009rishab-afk/CD-Mesh_S3-Meshtastic/Hardware/IMG/BAT-CHG.jpg

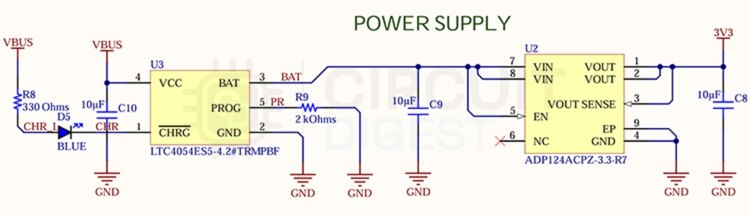
Hardware/IMG/BAT-CHG.jpg
