009rishab-afk/CD-Mesh_S3-Meshtastic/Hardware/IMG/Chat-Overview.png

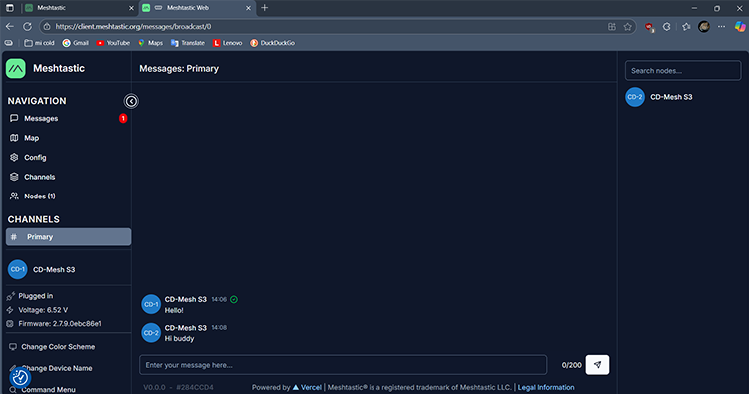
Hardware/IMG/Chat-Overview.png
