009rishab-afk/CD-Mesh_S3-Meshtastic/Hardware/IMG/Env-Select.png

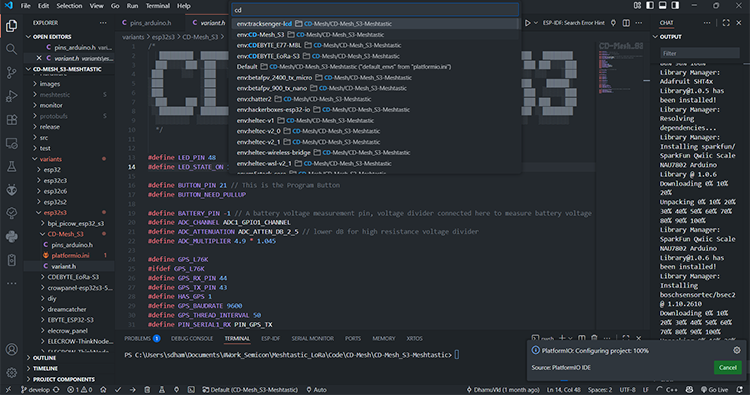
Hardware/IMG/Env-Select.png
