009rishab-afk/CD-Mesh_S3-Meshtastic/Hardware/IMG/ESP32S3-MCU.jpg

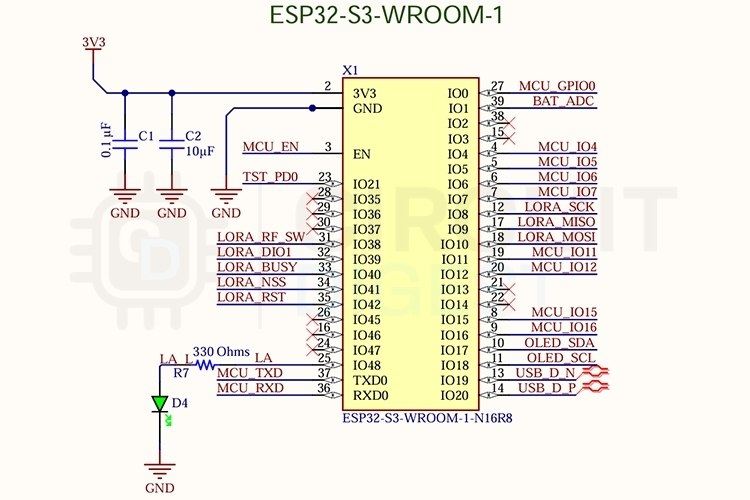
Hardware/IMG/ESP32S3-MCU.jpg
