009rishab-afk/CD-Mesh_S3-Meshtastic/Hardware/IMG/GPIO-Expander.jpg

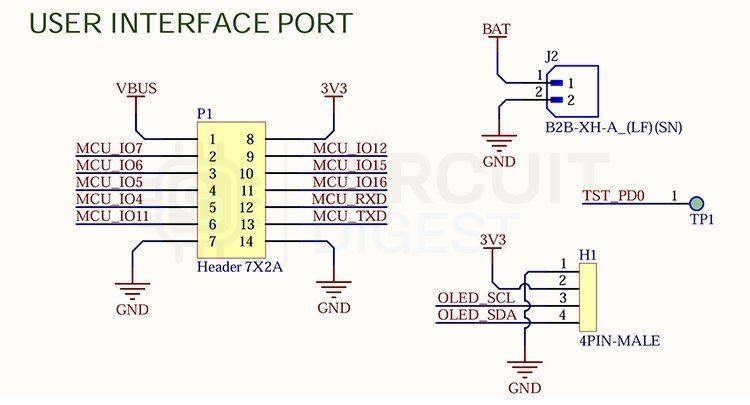
Hardware/IMG/GPIO-Expander.jpg
