009rishab-afk/CD-Mesh_S3-Meshtastic/Hardware/IMG/Interface.png

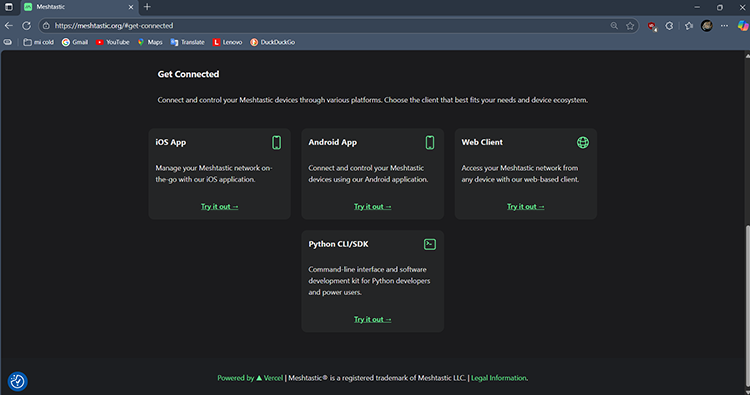
Hardware/IMG/Interface.png
