009rishab-afk/CD-Mesh_S3-Meshtastic/Hardware/IMG/JLCPCB.jpg

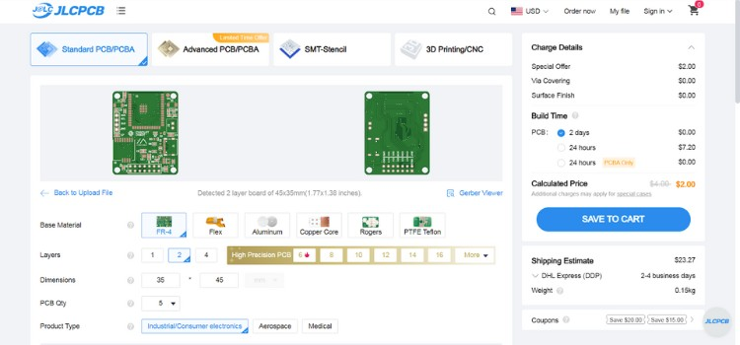
Hardware/IMG/JLCPCB.jpg
