009rishab-afk/CD-Mesh_S3-Meshtastic/Hardware/IMG/Part-View.jpg

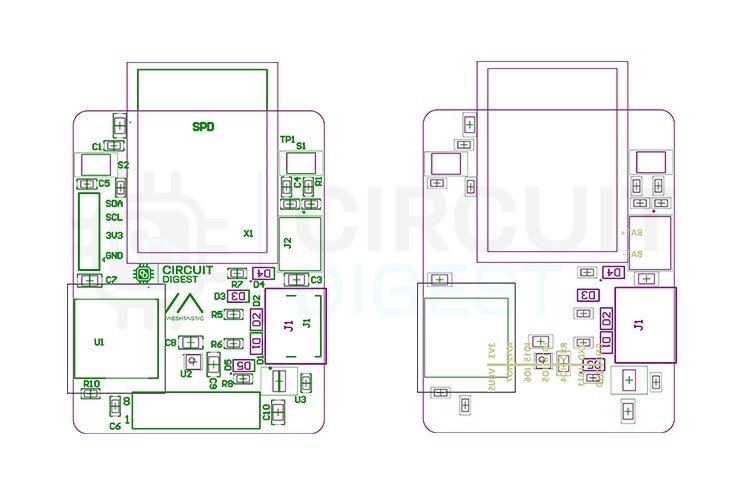
Hardware/IMG/Part-View.jpg
