009rishab-afk/CD-Mesh_S3-Meshtastic/Hardware/IMG/PCB-Overview.jpg

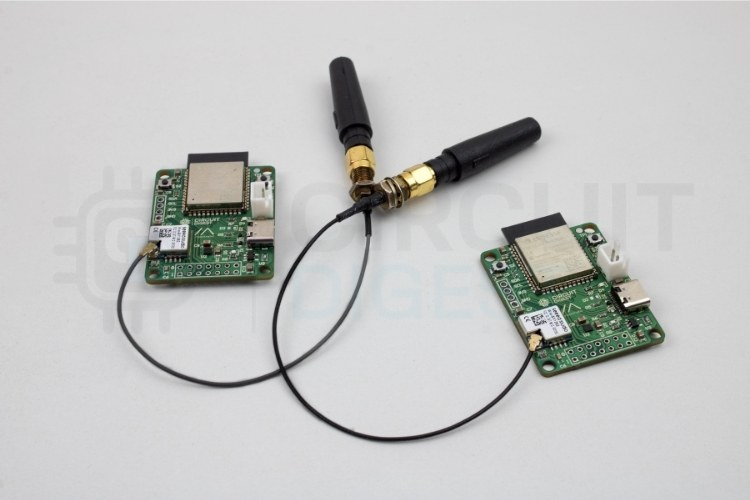
Hardware/IMG/PCB-Overview.jpg
