009rishab-afk/CD-Mesh_S3-Meshtastic/Hardware/IMG/Port-Select.png

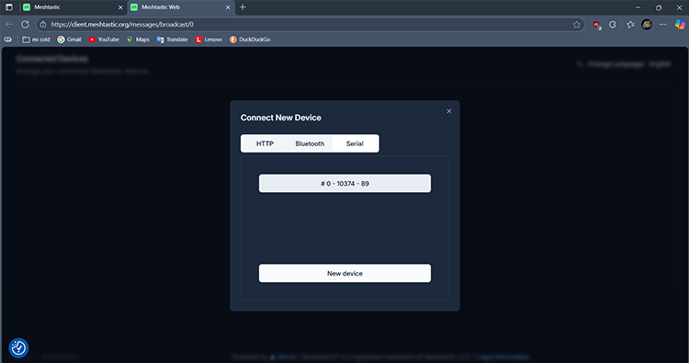
Hardware/IMG/Port-Select.png
