009rishab-afk/CD-Mesh_S3-Meshtastic/Hardware/IMG/Top-and-Bottom-Plane.jpg

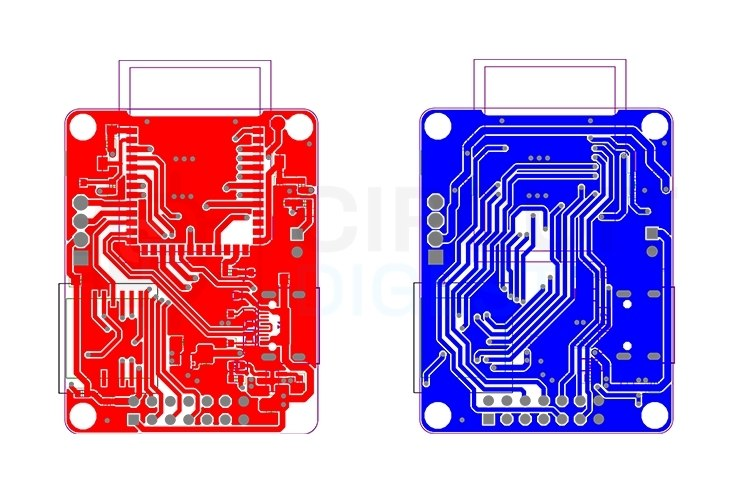
Hardware/IMG/Top-and-Bottom-Plane.jpg
