009rishab-afk/CD-Mesh_S3-Meshtastic/Hardware/IMG/WIO-SX1262.jpg

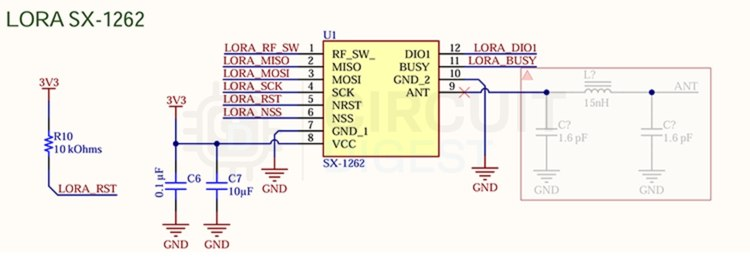
Hardware/IMG/WIO-SX1262.jpg
