009rishab-afk/CD-Mesh_S3-Meshtastic/Hardware/PCB/PCB_Board/Layers/Fab-6.png

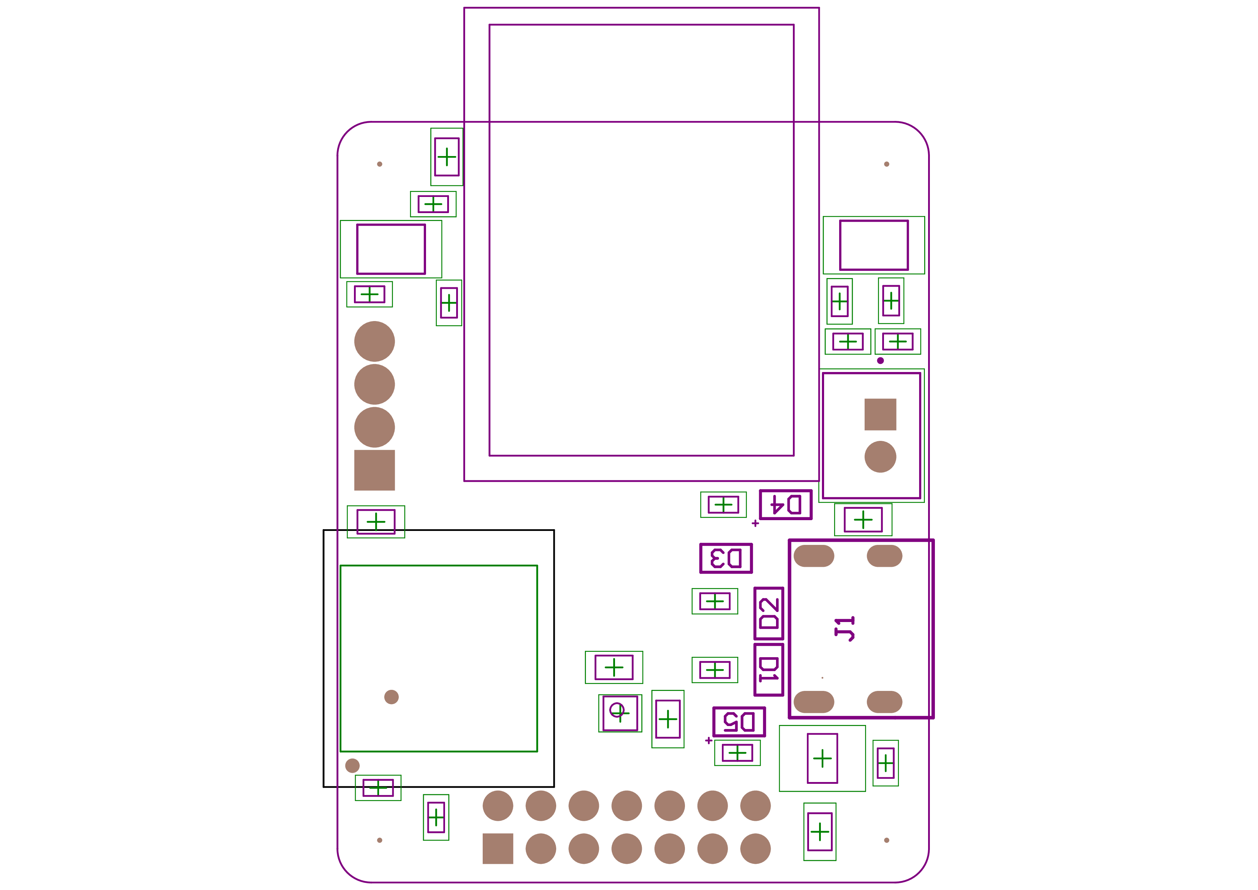
Hardware/PCB/PCB_Board/Layers/Fab-6.png
