009rishab-afk/CD-Mesh_S3-Meshtastic/Hardware/PCB/PCB_Board/PCB3-ESP32S3.png

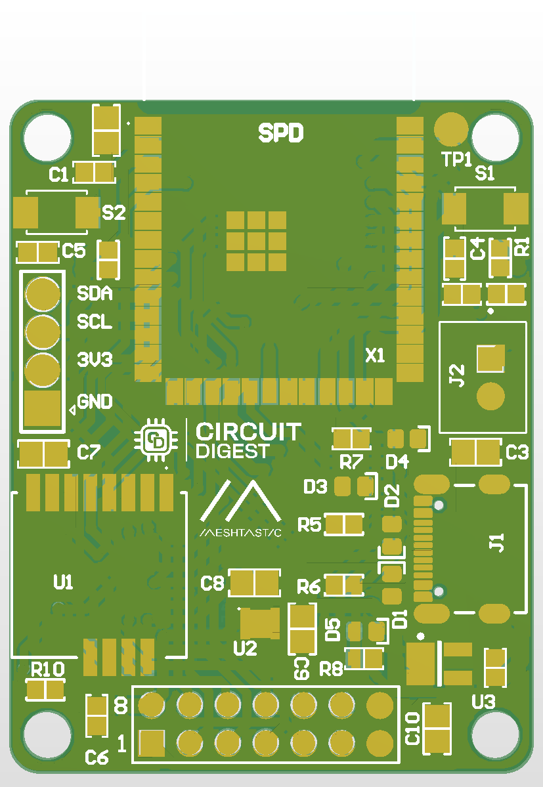
Hardware/PCB/PCB_Board/PCB3-ESP32S3.png
