009rishab-afk/CD-Mesh_S3-Meshtastic/Meshtatic-Working.gif

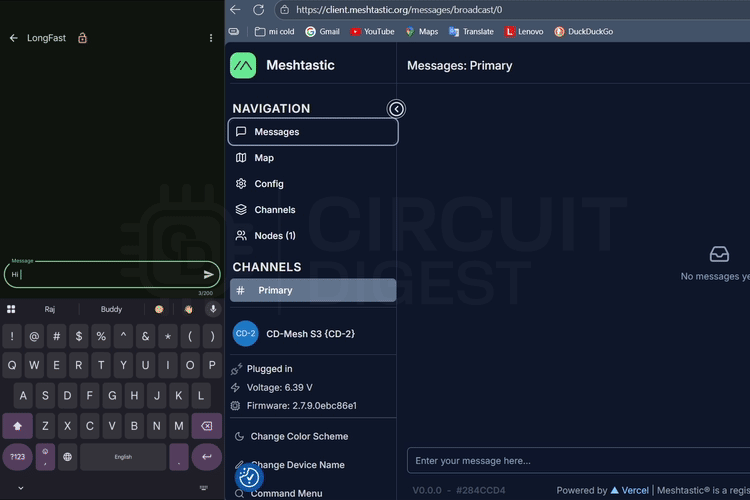
Meshtatic-Working.gif
