009rishab-afk/CD-Mesh_S3-Meshtastic/Hardware/IMG/Meshtastic-parts-marking.jpg

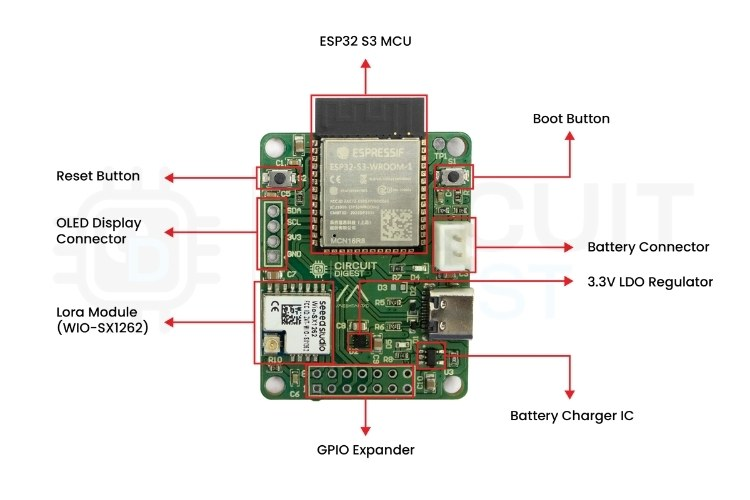
Hardware/IMG/Meshtastic-parts-marking.jpg
