009rishab-afk/CD-Mesh_S3-Meshtastic/Hardware/IMG/3D-Print.jpg

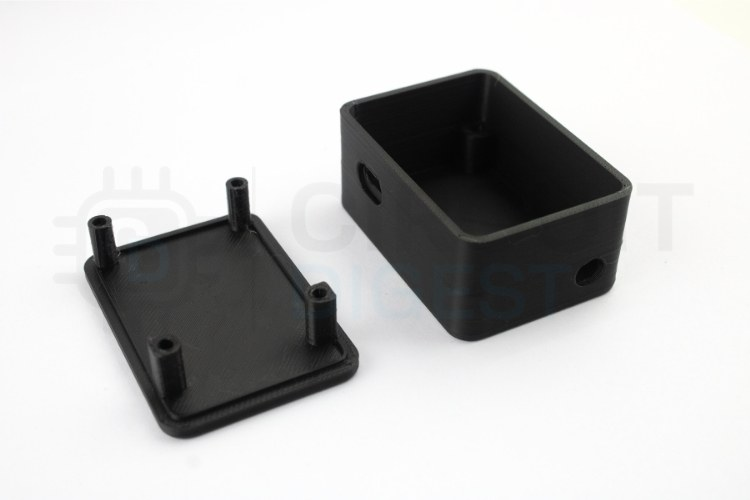
Hardware/IMG/3D-Print.jpg
