009rishab-afk/CD-Mesh_S3-Meshtastic/Hardware/IMG/PCB-Assembly.jpg

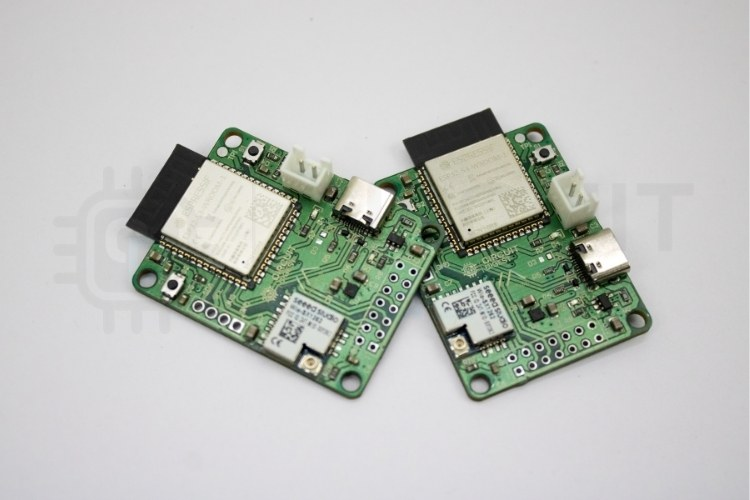
Hardware/IMG/PCB-Assembly.jpg
